cristianoag/uMSX/Cases/Acrylic_v2/uMSX_Case_Top.png

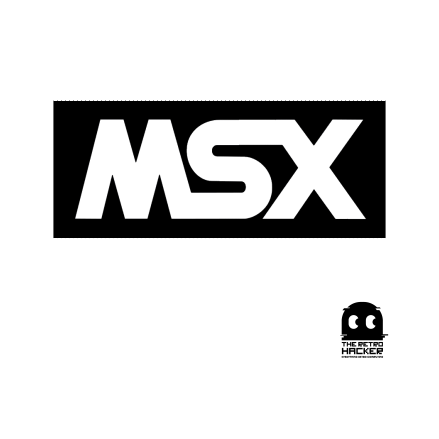
Cases/Acrylic_v2/uMSX_Case_Top.png
