cristianoag/uMSX/Schemas/ZemmixKR_sch.png

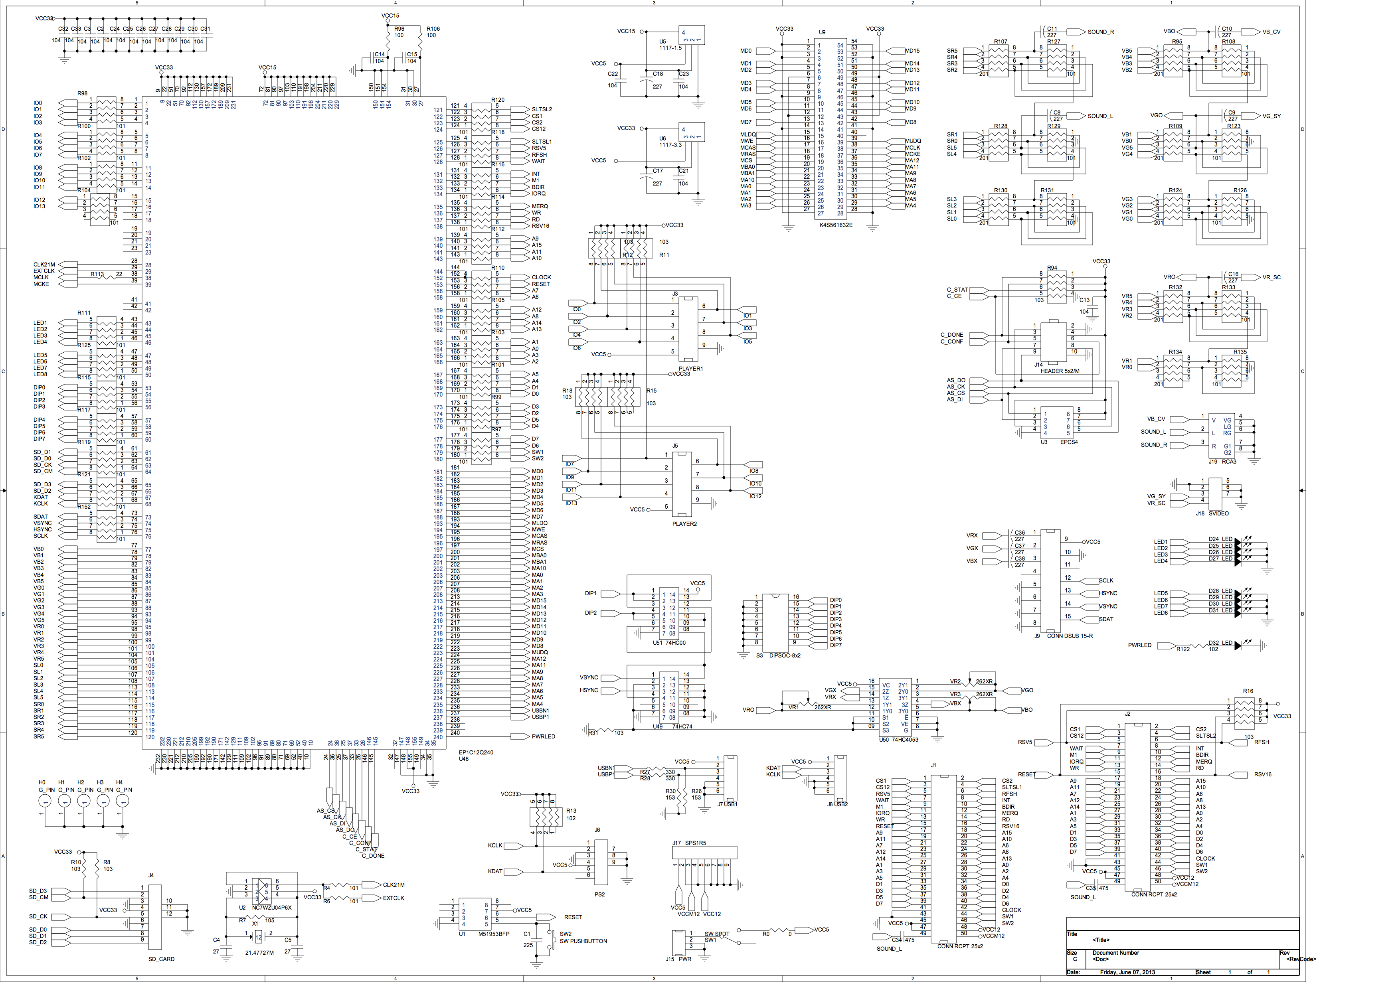
Schemas/ZemmixKR_sch.png
