cristianoag/uMSX/Manuals/20211118-210204.jpg

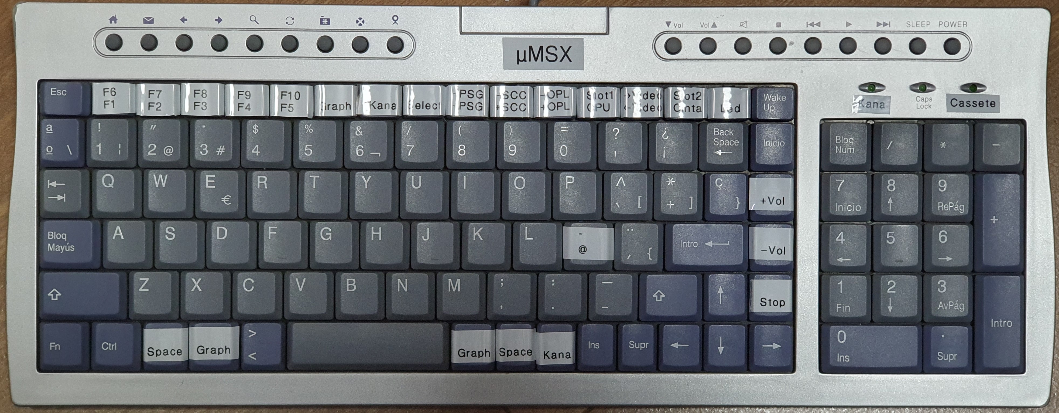
Manuals/20211118-210204.jpg
